Peter-Olsen-Hul-Igennem/DwarfMaster/src/Screen.cpp

#include "Screen.h"
#include "ButtonState.h"
#include <Fonts/FreeSansBold24pt7b.h>
#include <Fonts/FreeSansBold12pt7b.h>

Screen::Screen()
{
    tft.begin(0x9341);
    tft.setRotation(1); // landscape
    tft.fillScreen(TFT_BLACK);

    tft.setTextColor(TFT_DARKGREY);
    tft.setFont(&FreeSansBold24pt7b);
    tft.setTextSize(1);
    tft.setCursor(75, 100);
    tft.print("DWARF");
    tft.setCursor(60, 170);
    tft.print("MASTER");
    tft.setFont();
}

void Screen::showWaitScreen()
{
    tft.fillScreen(TFT_BLACK);

    tft.setTextColor(TFT_DARKGREY);
    tft.setTextSize(1);
    tft.setFont(&FreeSansBold12pt7b);
    tft.setCursor(10, 100);
    tft.print("PRESS A BUTTON WHEN");
    tft.setCursor(10, 150);
    tft.print("THE DWARF IS READY!");
    tft.setFont();

    Point p;
    ButtonState* btnState = btnState->getInstance();
    while (true)
    {
        p = touch.getTouchPoint();
        if (p.pressed)
        {
            return;
        }
        if (btnState->getSingleButtonPressed() > 0)
        {
            return;
        }
    }
}

void Screen::blankScreen()
{
    tft.fillScreen(TFT_BLACK);
}

void Screen::showMessage(const char* msg)
{
    Point p;
    ButtonState* btnState = btnState->getInstance();
    char message[85];
    char subString[17];
    uint8_t cnt = 0;
    uint8_t i;

    strlcpy(message, msg, 85);
    
    tft.fillScreen(BACKGROUND_COLOR);
    tft.setTextColor(TFT_BLACK);
    tft.setTextSize(3);
    
    while (strlen(message) > 0 && cnt < 6)
    {
        
        if (strlen(message) < 18)
        {
            tft.setCursor(10, 45 + (cnt * 35));
            tft.print(String(message));
            break;
        }

        i = 17;
        if (' ' != message[i])
        {
            i--;
            for (; i > 0; i--)
            {
                if (' ' == message[i])
                    break;
            }
        }
        
        memcpy(subString, message, (i) * sizeof(char));
        subString[i] = '\0';
        
        memcpy(&message[0], &message[i + 1] , (strlen(message) - i) * sizeof(char));

        tft.setCursor(10, 45 + (cnt * 35));
        tft.print(String(subString));
        
        cnt++;
    }

    touch.waitForTouchReleased();
    while (true)
    {
        p = touch.getTouchPoint();
        if (p.pressed)
        {
            return;
        }
        if (btnState->getSingleButtonPressed() == 1) // Footswitch 1: cancel
        {
            return;
        }
    }
}

void Screen::drawPlayButton(const uint8_t btnNbr, const bool patch, const bool selectedPatch, const bool btnStateFirst, const char* btnLabel, bool invertSelected)
{
    uint16_t bgColor  = TFT_LIGHTGREY;
    uint16_t txtColor = TFT_BLACK;
    uint8_t txtSize   = 3;
    if (patch)
    {
        if (selectedPatch && !invertSelected)
        {
            if (btnStateFirst)
            {
                bgColor  = TFT_BLUE;
                txtColor = TFT_WHITE;
            }
            else
            {
                bgColor  = TFT_RED;
                txtColor = TFT_WHITE;
            }
        }
    }
    else
    { // Toggle
        if (btnStateFirst)
        {
            bgColor  = TFT_BLACK;
            txtColor = TFT_WHITE;
        }
        else
        {
            bgColor  = TFT_CYAN;
            txtColor = TFT_BLACK;
        }
    }

    tft.setTextColor(txtColor);
    tft.setTextSize(txtSize);

    switch (btnNbr)
    {
        case 1:
            tft.fillRect(0, DISPLAY_HEIGHT - PLAY_BTN_LABEL_HEIGHT, PLAY_BTN_LABEL_WIDTH, PLAY_BTN_LABEL_HEIGHT, bgColor);
            printButtonLabel(BTN_OFFSET_X_1, BTN_OFFSET_Y_BTM, btnLabel, txtSize);
            break;
        case 2:
            tft.fillRect(PLAY_BTN_LABEL_WIDTH + LINE_WIDTH, DISPLAY_HEIGHT - PLAY_BTN_LABEL_HEIGHT, PLAY_BTN_LABEL_WIDTH, PLAY_BTN_LABEL_HEIGHT, bgColor);
            printButtonLabel(BTN_OFFSET_X_2, BTN_OFFSET_Y_BTM, btnLabel, txtSize);
            break;
        case 3:
            tft.fillRect(PLAY_BTN_LABEL_WIDTH + LINE_WIDTH + PLAY_BTN_LABEL_WIDTH + LINE_WIDTH, DISPLAY_HEIGHT - PLAY_BTN_LABEL_HEIGHT, PLAY_BTN_LABEL_WIDTH, PLAY_BTN_LABEL_HEIGHT, bgColor);
            printButtonLabel(BTN_OFFSET_X_3, BTN_OFFSET_Y_BTM, btnLabel, txtSize);
            break;
        case 4:
            tft.fillRect(0, 0, PLAY_BTN_LABEL_WIDTH, PLAY_BTN_LABEL_HEIGHT, bgColor);
            printButtonLabel(BTN_OFFSET_X_1, BTN_OFFSET_Y_TOP, btnLabel, txtSize);
            break;
        case 5:
            tft.fillRect(PLAY_BTN_LABEL_WIDTH + LINE_WIDTH, 0, PLAY_BTN_LABEL_WIDTH, PLAY_BTN_LABEL_HEIGHT, bgColor);
            printButtonLabel(BTN_OFFSET_X_2, BTN_OFFSET_Y_TOP, btnLabel, txtSize);
            break;
        case 6:
            tft.fillRect(PLAY_BTN_LABEL_WIDTH + LINE_WIDTH + PLAY_BTN_LABEL_WIDTH + LINE_WIDTH, 0, PLAY_BTN_LABEL_WIDTH, PLAY_BTN_LABEL_HEIGHT, bgColor);
            printButtonLabel(BTN_OFFSET_X_3, BTN_OFFSET_Y_TOP, btnLabel, txtSize);
            break;

        default:
            break;
    }
}

void Screen::printButtonLabel(const uint16_t offsetX, const uint16_t offsetY, const char* btnLabel, const uint8_t textSize)
{
    size_t maxNbrOfChars = 5;
    size_t labelSize     = strlen(btnLabel);
    uint8_t xPosOffset   = 0;
    char txt[maxNbrOfChars + 1];
    if (labelSize < maxNbrOfChars + 1)
    {
        strncpy(txt, &btnLabel[0], maxNbrOfChars);
        for (size_t i = maxNbrOfChars; i > 0; i--)
        {
            if (txt[i - 1] != ' ')
            {
                txt[i] = '\0';
                break;
            }
        }
        xPosOffset = getXposOffset(txt, maxNbrOfChars, textSize);
        tft.setCursor(offsetX + xPosOffset, offsetY + 14);
        tft.print(String(txt));
    }
    else
    {
        strncpy(txt, &btnLabel[0], maxNbrOfChars);
        for (size_t i = maxNbrOfChars; i > 0; i--)
        {
            if (txt[i - 1] != ' ')
            {
                txt[i] = '\0';
                break;
            }
        }
        xPosOffset = getXposOffset(txt, maxNbrOfChars, textSize);
        tft.setCursor(offsetX + xPosOffset, offsetY);
        tft.print(String(txt));

        strncpy(txt, &btnLabel[maxNbrOfChars], maxNbrOfChars);
        for (size_t i = maxNbrOfChars; i > 0; i--)
        {
            if (txt[i - 1] != ' ')
            {
                txt[i] = '\0';
                break;
            }
        }
        xPosOffset = getXposOffset(txt, maxNbrOfChars, textSize);
        tft.setCursor(offsetX + xPosOffset, offsetY + 28);
        tft.print(String(txt));
    }
}

void Screen::drawPlayBank(const char* bnkNbr, const char* bnkName, const bool inverted)
{
    uint16_t bgColor  = TFT_BLACK;
    uint16_t txtColor = TFT_WHITE;
    if (inverted)
    {
        bgColor  = TFT_WHITE;
        txtColor = TFT_BLACK;
    }
    tft.fillRect(0, BANK_OFFSET_Y - 10, DISPLAY_WIDTH, DISPLAY_HEIGHT - 160, bgColor);

    tft.setCursor(5, BANK_OFFSET_Y);
    tft.setTextColor(txtColor);
    tft.setTextSize(8);
    tft.print(String(bnkNbr));

    tft.setCursor(PLAY_BTN_LABEL_WIDTH, BANK_OFFSET_Y + 28);
    tft.setTextSize(4);
    tft.print(String(bnkName));
}

String Screen::getKeyboardInputFromUser(const String* contextLabel, const String* oldText, const byte maxLength)
{
    return alphaTouchKeyb.getInputFromUser(contextLabel, oldText, maxLength);
}

uint16_t Screen::getNumKeyboardInputFromUser(const String* contextLabel, const String* oldVal, const byte maxLength)
{
    uint16_t result = 0;
    String newVal   = numTouchKeyb.getInputFromUser(contextLabel, oldVal, maxLength);
    result          = newVal.toInt();
    return result;
}

bool Screen::playBankPressed()
{
    Point p = touch.getTouchPoint();
    if (p.pressed)
    {
        if (p.y > BANK_OFFSET_Y && p.y < DISPLAY_HEIGHT - BANK_OFFSET_Y)
            return true;
    }
    return false;
}

uint8_t Screen::playBtnPressed()
{
    Point p = touch.getTouchPoint();
    if (p.pressed)
    {
        if (p.y < PLAY_BTN_LABEL_HEIGHT)
        {
            if (p.x < PLAY_BTN_LABEL_WIDTH)
                return 4;
            else if (p.x < (PLAY_BTN_LABEL_WIDTH * 2 + LINE_WIDTH))
                return 5;
            else
                return 6;
        }
        else if (p.y > DISPLAY_HEIGHT - PLAY_BTN_LABEL_HEIGHT)
        {
            if (p.x < PLAY_BTN_LABEL_WIDTH)
                return 1;
            else if (p.x < (PLAY_BTN_LABEL_WIDTH * 2 + LINE_WIDTH))
                return 2;
            else
                return 3;
        }
    }
    return 0;
}

int Screen::getButtonPushed()
{
    uint16_t cnt   = 0;
    int prevButton = -2;
    int button     = -1;

    ButtonState* btnState = btnState->getInstance();

    Point p;
    while (true)
    {
        p = touch.getTouchPoint();
        if (p.pressed)
        {
            button = mapPointToBtn(p);
            if (button != prevButton)
            {
                cnt        = 0;
                prevButton = button;
            }
            else
            {
                cnt++;
                if (cnt > 100 && button != -1)
                    break;
            }
        }
        if (btnState->getSingleButtonPressed() == 1) // Footswitch 1: cancel
        {
            return 0;
        }
    }
    return button;
}

void Screen::waitForButtonReleased()
{
    touch.waitForTouchReleased();
    return;
}

void Screen::drawEdit(const char* label, const EditLabelAttributes* btnLabels)
{
    drawEditGrid();
    printEditLabel(label);
    printEditButtonLabels(btnLabels);
}

void Screen::drawEditGrid()
{
    tft.fillScreen(BACKGROUND_COLOR);

    int x;
    int y;
    for (int j = 1; j < 4; j++)
    {
        y = Y_SIZE * j;
        for (int i = 0; i < 3; i++)
        {
            tft.drawLine(0, y + i, DISPLAY_WIDTH, y + i, LINE_COLOR);
        }
        x = X_SIZE * j;
        if (j < 3)
        {
            for (int i = 0; i < 3; i++)
            {
                tft.drawLine(x + i, 60, x + i, DISPLAY_HEIGHT, LINE_COLOR);
            }
        }
    }
}

void Screen::printEditLabel(const char* label)
{
    tft.setCursor(10, 17);
    tft.setTextColor(TFT_BLACK);
    tft.setTextSize(4);
    tft.print(String(label));
}

void Screen::printEditButtonLabels(const EditLabelAttributes* labels)
{
    tft.setTextColor(TFT_BLACK);
    tft.setTextSize(2);
    uint8_t cnt     = 0;
    uint16_t y      = 0;
    uint16_t x      = 0;
    uint8_t xOffset = 0;
    for (uint8_t j = 1; j < 4; j++)
    {
        y = 15 + (Y_SIZE * j);
        for (uint8_t i = 0; i < 3; i++)
        {
            x = 7 + (X_SIZE * i);
            tft.fillRect(x, y, 95, 40, BACKGROUND_COLOR);
            tft.setTextSize(2);
            xOffset = getXposOffset(labels[cnt].label1, 8, 2);
            tft.setCursor(x + xOffset, y);
            tft.print(labels[cnt].label1);
            tft.setTextSize(1);
            xOffset = getXposOffset(labels[cnt].label2, 16, 1);
            tft.setCursor(x + xOffset, y + 25);
            tft.print(labels[cnt].label2);
            if (labels[cnt].color > 0)
                tft.fillRect(x, y + 25, 95, 5, labels[cnt].color);
            cnt++;
        }
    }
}

bool Screen::getBinaryInputFromUser(const char* label1, const char* label2, const bool firstIsTrue)
{
    bool prevChoice = firstIsTrue;
    bool newChoice  = firstIsTrue;

    drawBinaryEdit(label1, label2, firstIsTrue);

    waitForButtonReleased();

    ButtonState* btnState = btnState->getInstance();
    Point p;
    while (true)
    {
        p = touch.getTouchPoint();
        if (p.pressed)
        {
            if (p.y < DISPLAY_HEIGHT / 2)
                newChoice = true;
            else
                newChoice = false;

            if (prevChoice != newChoice)
            {
                drawBinaryEdit(label1, label2, newChoice);
                waitForButtonReleased();
                break;
            }
            else
            {
                waitForButtonReleased();
                break;
            }
        }
        if (btnState->getSingleButtonPressed() == 1) // Footswitch 1: cancel
        {
            return firstIsTrue;
        }
    }
    return newChoice;
}

void Screen::drawBinaryEdit(const char* label1, const char* label2, bool firstIsTrue)
{
    tft.fillScreen(BACKGROUND_COLOR);
    if (firstIsTrue)
        tft.fillRect(0, 0, DISPLAY_WIDTH, DISPLAY_HEIGHT / 2, TFT_GREEN);
    else
        tft.fillRect(0, DISPLAY_HEIGHT / 2, DISPLAY_WIDTH, DISPLAY_HEIGHT, TFT_RED);

    for (size_t i = 0; i < 5; i++)
    {
        tft.drawLine(0, DISPLAY_HEIGHT / 2 - 2 + i, DISPLAY_WIDTH, DISPLAY_HEIGHT / 2 - 2 + i, TFT_BLACK);
    }

    tft.setTextColor(TFT_BLACK);
    tft.setTextSize(4);
    tft.setCursor(10, 45);
    tft.print(String(label1));
    tft.setCursor(10, 165);
    tft.print(String(label2));
}

uint8_t Screen::mapPointToBtn(Point point)
{
    if (point.y < Y_SIZE)
        return -1;

    uint8_t x = point.x / X_SIZE + 1;
    uint8_t y = point.y / Y_SIZE - 1;

    return x + (3 * y);
}

uint8_t Screen::getXposOffset(const char* label, const uint8_t maxNbrOfChars, const uint8_t textSize)
{
    uint16_t result = 0;
    // int16_t x;
    // int16_t y;
    uint16_t w;
    // uint16_t h;
    uint8_t dif             = maxNbrOfChars - strlen(label);
    bool difIsAnEqualNumber = true;

    if (dif % 2 == 1)
        difIsAnEqualNumber = false;

    dif = dif / 2;

    // tft.setTextSize(textSize);
    // tft.getTextBounds("X", 0, 0, &x, &y, &w, &h);
    w      = textSize * 6;
    result = dif * w;
    if (!difIsAnEqualNumber)
        result += w / 2;

    return result;
}
