Peter-Olsen-Hul-Igennem/DwarfMaster/src/Touch.cpp

#include "Touch.h"

Touch::Touch()
{
}

Point Touch::getTouchPoint()
{
    Point p;
    p.x         = -1;
    p.y         = -1;
    p.pressed   = false;
    TSPoint tsp = ts.getPoint();
    pinMode(YP, OUTPUT); // restore shared pins
    pinMode(XM, OUTPUT);
    digitalWrite(YP, HIGH); // because TFT control pins
    digitalWrite(XM, HIGH);

    if (tsp.x > 940 || tsp.y > 880)
        return p;

    if (tsp.z > MINPRESSURE && tsp.z < MAXPRESSURE)
    {
        p.pressed = true;
        p.x = map(tsp.y, TS_TOP, TS_BOT, 0, 320);
        p.y = map(tsp.x, TS_RT, TS_LEFT, 0, 240);
    }
    return p;
}

void Touch::waitForTouchReleased()
{
    Point p;
    uint16_t cnt = 0;
    while (true)
    {
        p = getTouchPoint();
        if (p.pressed)
        {
            cnt = 0;
        }
        else
        {
            cnt++;
            if (cnt > 500)
                break;
        }
    }
    return;
}
